sandgum/Triangulate-ES_01-Watch/CAD/Components (DON'T PRINT)/100mah battery (4).step

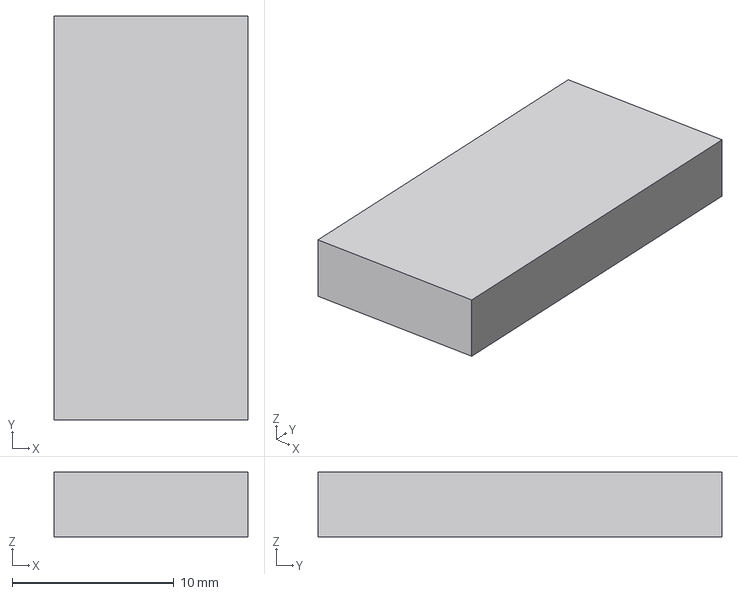
[picture p16: CAD file, 2026-01-16]
CAD/Components (DON'T PRINT)/100mah battery (4).step
12.0 x 25.0 x 4.00 mm
