sandgum/Triangulate-ES_01-Watch/CAD/Components (DON'T PRINT)/Button.step

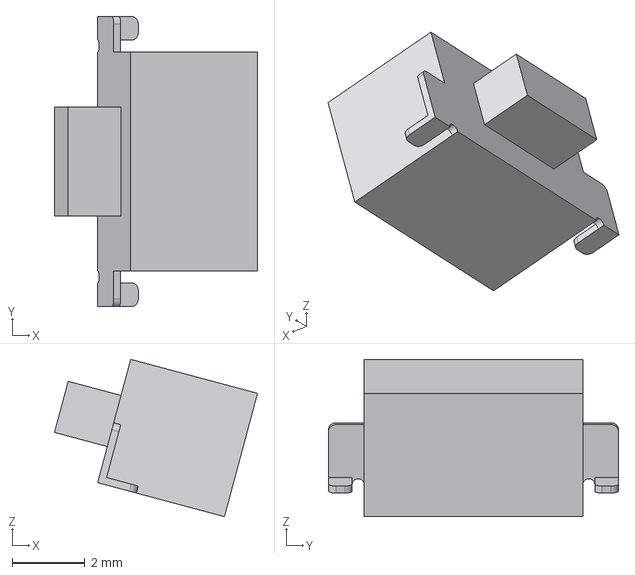
[picture p17: CAD file, 2026-01-16]
CAD/Components (DON'T PRINT)/Button.step
5.57 x 7.95 x 4.31 mm
