sandgum/Triangulate-ES_01-Watch/CAD/Components (DON'T PRINT)/oled display (1).step

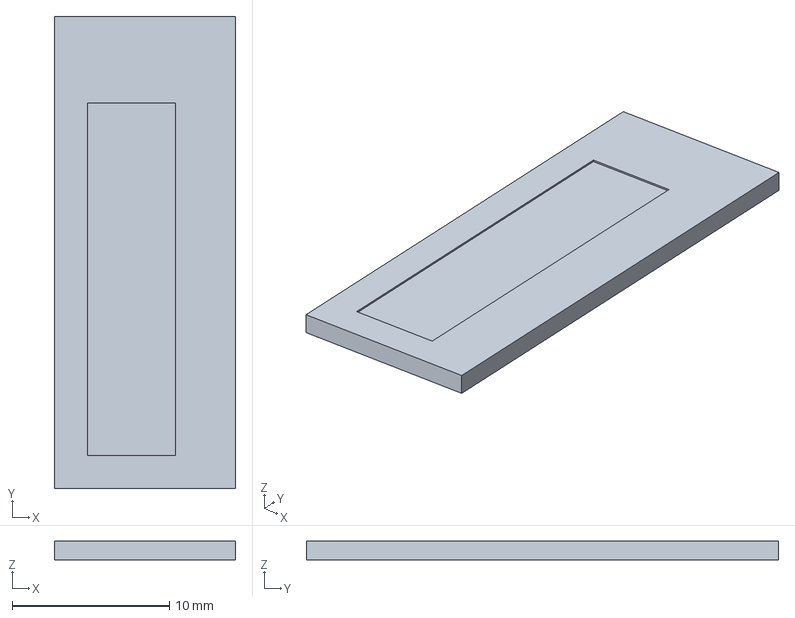
[picture p18: CAD file, 2026-01-16]
CAD/Components (DON'T PRINT)/oled display (1).step
11.5 x 30.0 x 1.20 mm
