sandgum/Triangulate-ES_01-Watch/CAD/Components (DON'T PRINT)/haptic motor.step

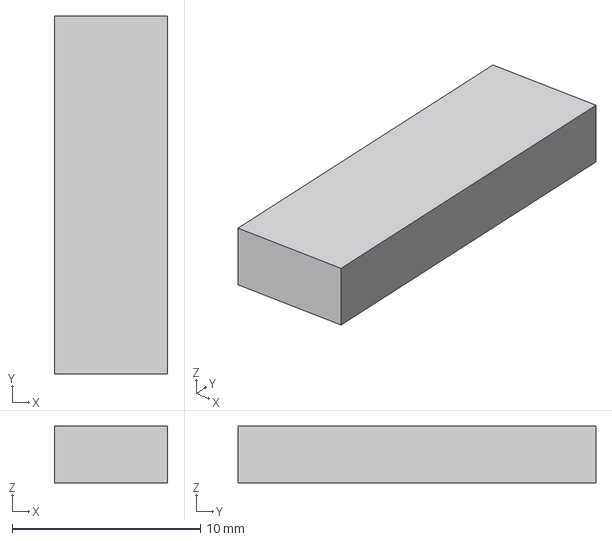
[picture p19: CAD file, 2026-01-16]
CAD/Components (DON'T PRINT)/haptic motor.step
6.00 x 19.0 x 3.00 mm
