sandgum/Triangulate-ES_01-Watch/CAD/Components (DON'T PRINT)/e ink display.step

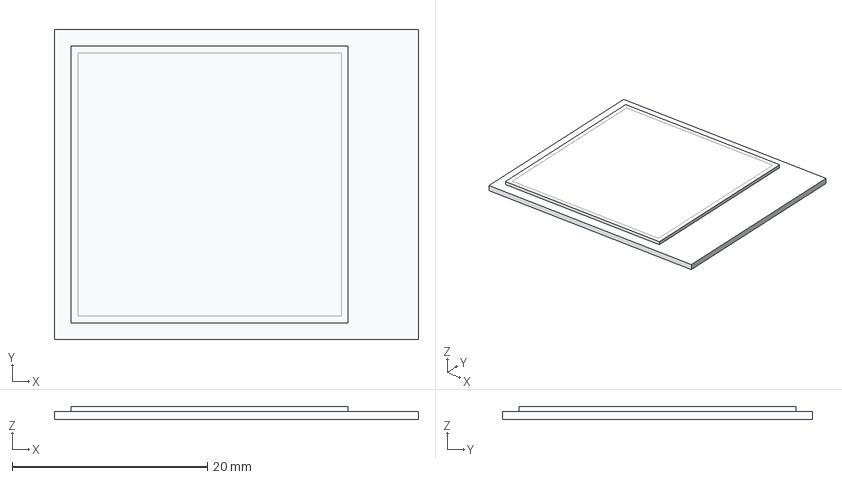
[picture p20: CAD file, 2026-01-16]
CAD/Components (DON'T PRINT)/e ink display.step
37.3 x 31.8 x 1.35 mm
