sandgum/Triangulate-ES_01-Watch/KiCad Files V1/E-ink watch.kicad_sch

## KiCad design KiCad Files V1/E-ink watch.kicad_sch (2025-12-14)

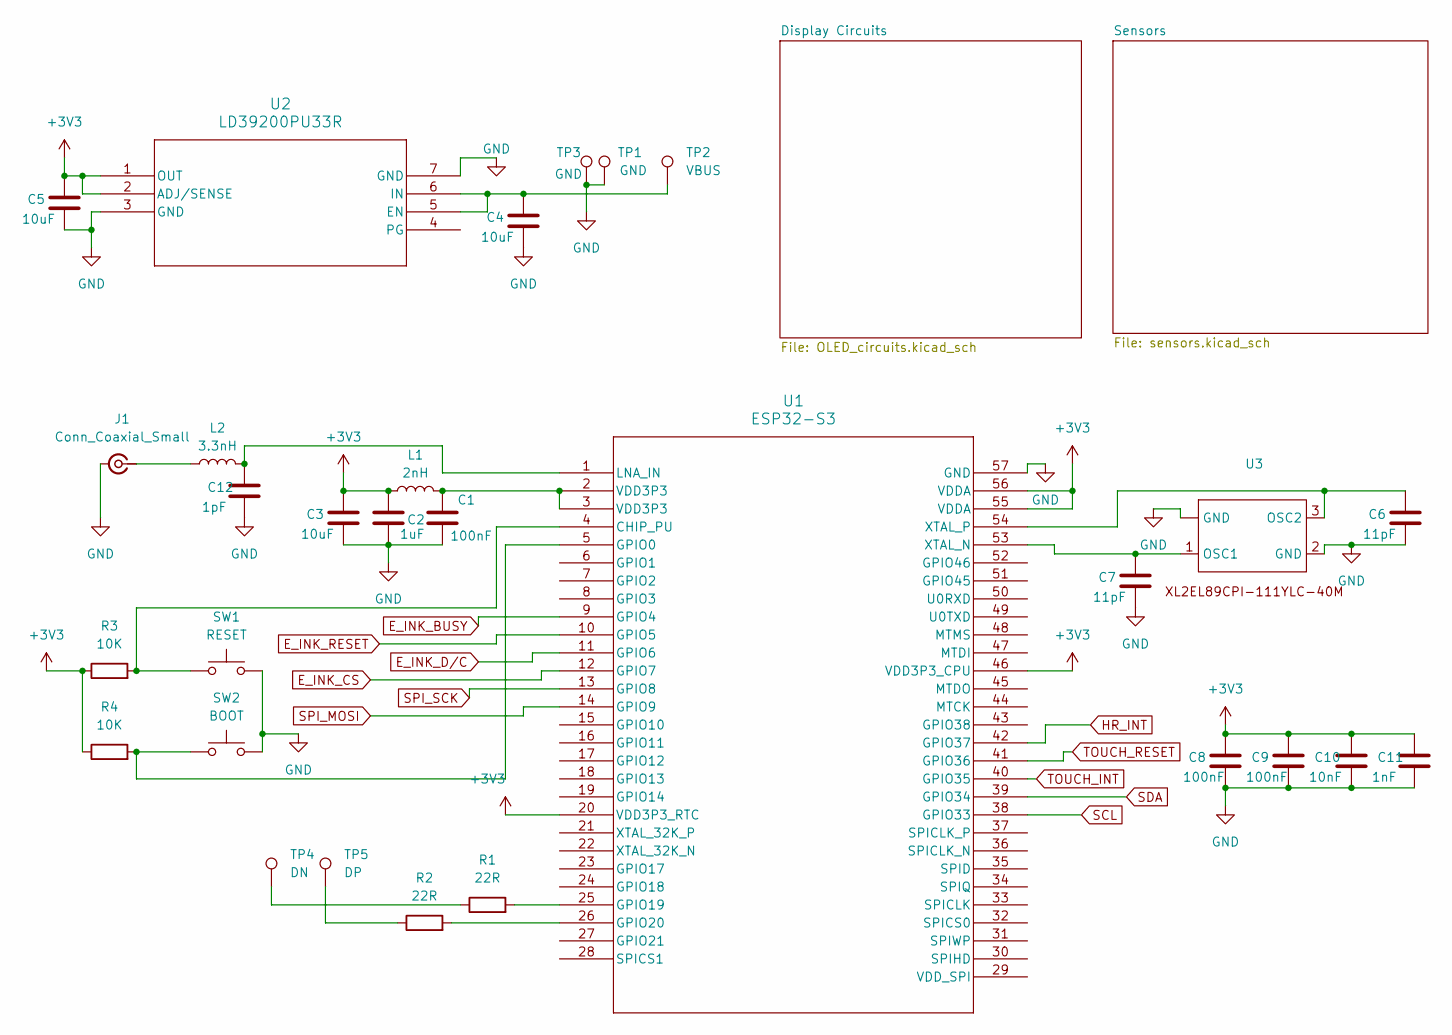
[picture p35: schematic E-ink watch.kicad_sch]

Parts:
C1, C8, C9: 100nF
C2: 1uF
C3, C4, C5: 10uF
C6, C7: 11pF
C10: 10nF
C11: 1nF
C12: 1pF
J1: Conn_Coaxial_Small
L1: 2nH
L2: 3.3nH
R1, R2: 22R
R3, R4: 10K
SW1: RESET
SW2: BOOT
TP1, TP3: GND
TP2: VBUS
TP4: DN
TP5: DP
U1: ESP32-S3; QFN56_7X7_EXP
U2: LD39200PU33R; SON_DFN6_3X3_STM
U3: (no value)

Connections:
+3V3: C2.1, C3.1, C5.1, C8.1, C9.1, C10.1, C11.1, L1.1, R3.1, R4.1, U1.20 (VDD3P3_RTC), U1.46 (VDD3P3_CPU), U1.55 (VDDA), U1.56 (VDDA), U2.1 (OUT), U2.2 (ADJ/SENSE)
E_INK_BUSY: U1.9 (GPIO4)
E_INK_CS: U1.12 (GPIO7)
E_INK_D/C: U1.11 (GPIO6)
E_INK_RESET: U1.10 (GPIO5)
GND: C1.2, C2.2, C3.2, C4.2, C5.2, C6.2, C7.2, C8.2, C9.2, C10.2, C11.2, C12.2, J1.2 (Ext), SW1.2, SW2.2, TP1.1, TP3.1, U1.57 (GND), U2.3 (GND), U2.7 (GND), U3. (GND), U3.2 (GND)
HR_INT: U1.42 (GPIO37)
unnamed: C1.1, L1.2, U1.2 (VDD3P3), U1.3 (VDD3P3)
unnamed: C4.1, TP2.1, U2.5 (EN), U2.6 (IN)
unnamed: C6.1, U1.54 (XTAL_P), U3.3 (OSC2)
unnamed: C7.1, U1.53 (XTAL_N), U3.1 (OSC1)
unnamed: C12.1, L2.2, U1.1 (LNA_IN)
unnamed: J1.1 (In), L2.1
unnamed: R1.1, TP4.1
unnamed: R1.2, U1.25 (GPIO19)
unnamed: R2.1, TP5.1
unnamed: R2.2, U1.26 (GPIO20)
unnamed: R3.2, SW1.1, U1.4 (CHIP_PU)
unnamed: R4.2, SW2.1, U1.5 (GPIO0)
SCL: U1.38 (GPIO33)
SDA: U1.39 (GPIO34)
SPI_MOSI: U1.14 (GPIO9)
SPI_SCK: U1.13 (GPIO8)
TOUCH_INT: U1.40 (GPIO35)
TOUCH_RESET: U1.41 (GPIO36)
