sandgum/Triangulate-ES_01-Watch/KiCad Files V1/OLED_circuits.kicad_sch

## KiCad design KiCad Files V1/OLED_circuits.kicad_sch (2025-12-14)

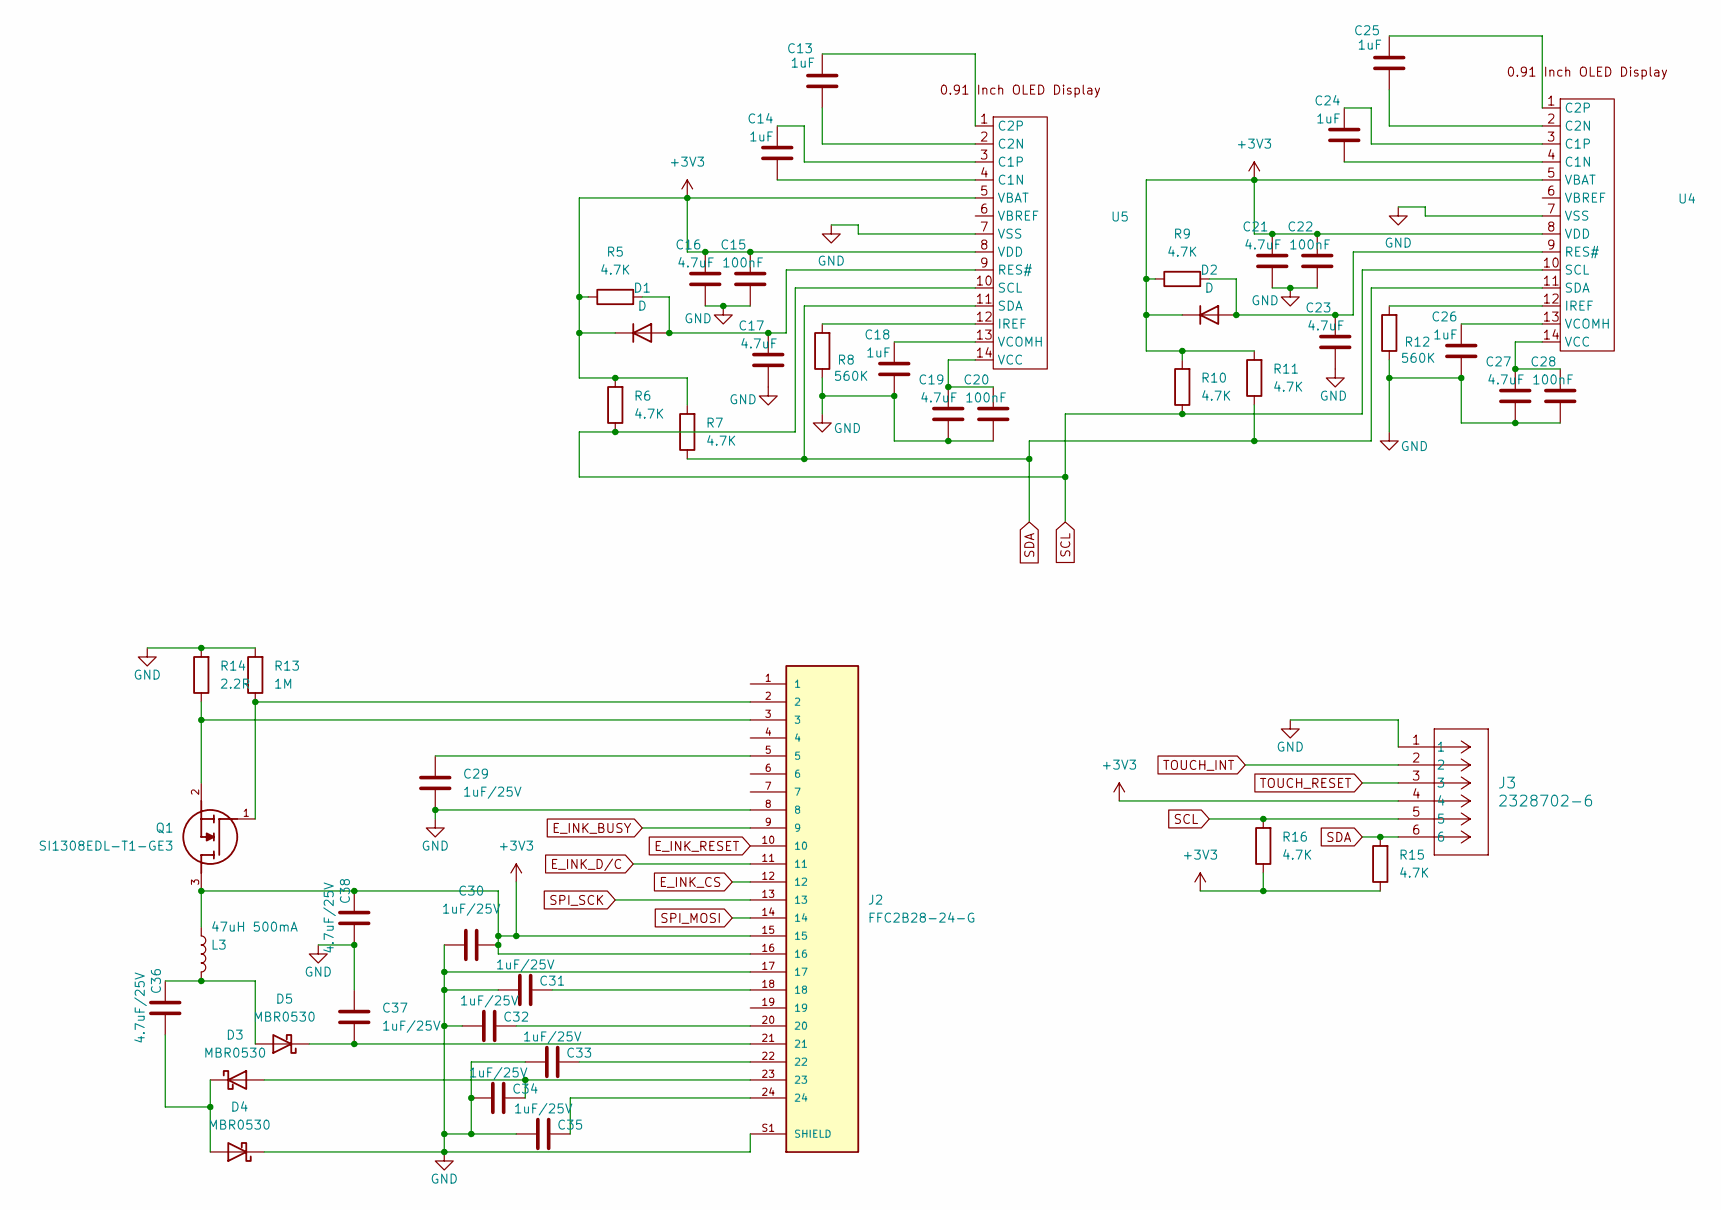
[picture p36: schematic OLED_circuits.kicad_sch]

Parts:
C13, C14, C18, C24, C25, C26: 1uF
C15, C20, C22, C28: 100nF
C16, C17, C19, C21, C23, C27: 4.7uF
C29, C30, C31, C32, C33, C34, C35, C37: 1uF/25V
C36, C38: 4.7uF/25V
D1, D2: D
D3, D4, D5: MBR0530
J2: FFC2B28-24-G; GCT_FFC2B28-24-G; PARTREV A
J3: 2328702-6; CONN6_2328702-6_TEC
L3: 47uH 500mA
Q1: SI1308EDL-T1-GE3; SOT65P210X110-3N; Mouser_Part_Number 78-SI1308EDL-T1-GE3
R5, R6, R7, R9, R10, R11, R15, R16: 4.7K
R8, R12: 560K
R13: 1M
R14: 2.2R
U4, U5: (no value)

Connections:
+3V3: C15.1, C16.1, C21.1, C22.1, C30.2, C38.2, D1.1 (K), D2.1 (K), J2.15, J2.16, J3.4, L3.1, Q1.3, R5.1, R6.2, R7.2, R9.1, R10.2, R11.2, R15.1, R16.1, U4.5 (VBAT), U4.8 (VDD), U5.5 (VBAT), U5.8 (VDD)
E_INK_BUSY: J2.9
E_INK_CS: J2.12
E_INK_D/C: J2.11
E_INK_RESET: J2.10
GND: C15.2, C16.2, C17.2, C18.2, C19.2, C20.2, C21.2, C22.2, C23.2, C26.2, C27.2, C28.2, C29.2, C30.1, C31.1, C32.1, C33.1, C34.1, C35.1, C37.1, C38.1, D4.1 (K), J2.8, J2.17, J2.S1 (SHIELD), J2.S2 (SHIELD), J3.1, R8.1, R12.1, R13.2, R14.2, U4.7 (VSS), U5.7 (VSS)
unnamed: C13.1, U5.1 (C2P)
unnamed: C13.2, U5.2 (C2N)
unnamed: C14.1, U5.3 (C1P)
unnamed: C14.2, U5.4 (C1N)
unnamed: C17.1, D1.2 (A), R5.2, U5.9 (RES#)
unnamed: C18.1, U5.13 (VCOMH)
unnamed: C19.1, C20.1, U5.14 (VCC)
unnamed: C23.1, D2.2 (A), R9.2, U4.9 (RES#)
unnamed: C24.1, U4.3 (C1P)
unnamed: C24.2, U4.4 (C1N)
unnamed: C25.1, U4.1 (C2P)
unnamed: C25.2, U4.2 (C2N)
unnamed: C26.1, U4.13 (VCOMH)
unnamed: C27.1, C28.1, U4.14 (VCC)
unnamed: C29.1, J2.5
unnamed: C31.2, J2.18
unnamed: C32.2, J2.20
unnamed: C33.2, J2.22
unnamed: C34.2, D3.2 (A), J2.23
unnamed: C35.2, J2.24
unnamed: C36.1, D3.1 (K), D4.2 (A)
unnamed: C36.2, D5.2 (A), L3.2
unnamed: C37.2, D5.1 (K), J2.21
unnamed: J2.2, Q1.1, R13.1
unnamed: J2.3, Q1.2, R14.1
unnamed: R8.2, U5.12 (IREF)
unnamed: R12.2, U4.12 (IREF)
SCL: J3.5, R6.1, R10.1, R16.2, U4.10 (SCL), U5.10 (SCL)
SDA: J3.6, R7.1, R11.1, R15.2, U4.11 (SDA), U5.11 (SDA)
SPI_MOSI: J2.14
SPI_SCK: J2.13
TOUCH_INT: J3.2
TOUCH_RESET: J3.3
