sandgum/Triangulate-ES_01-Watch/KiCad Files V1/sensors.kicad_sch

## KiCad design KiCad Files V1/sensors.kicad_sch (2025-12-14)

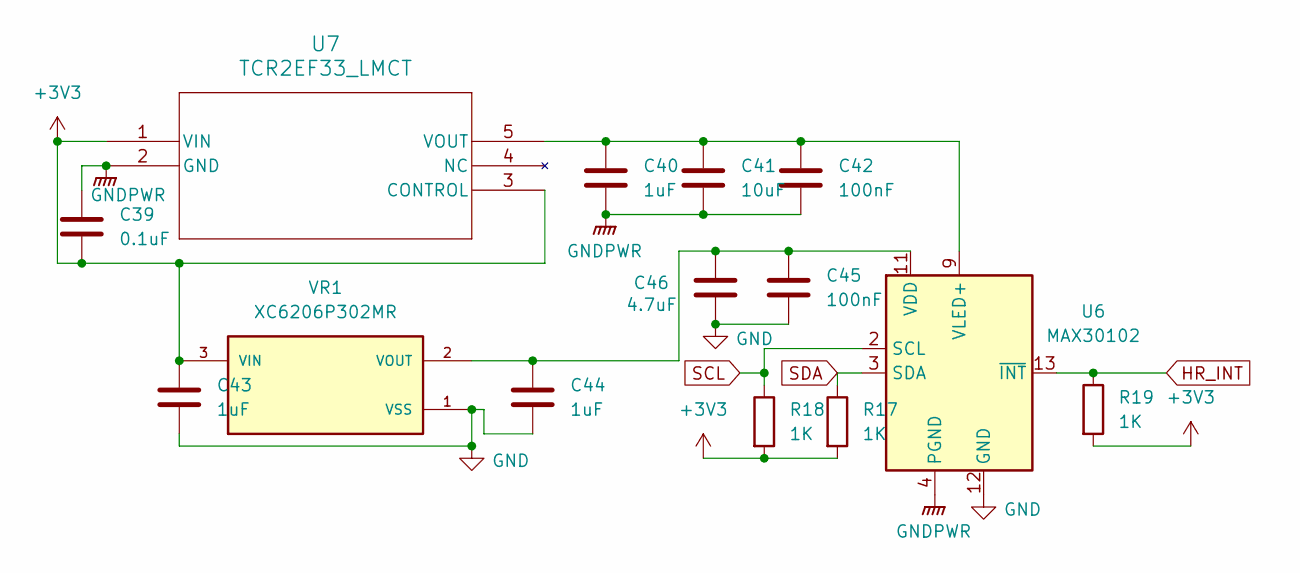
[picture p37: schematic sensors.kicad_sch]

Parts:
C39: 0.1uF
C40, C43, C44: 1uF
C41: 10uF
C42, C45: 100nF
C46: 4.7uF
R17, R18, R19: 1K
U6: MAX30102; Maxim_OLGA-14_3.3x5.6mm_P0.8mm
U7: TCR2EF33_LMCT; SOT-25 SMV_TOS
VR1: XC6206P302MR; SOT95P280X130-3N; PARTREV N/A

Connections:
+3V3: C39.2, C43.1, R17.2, R18.2, R19.2, U7.1 (VIN), U7.3 (CONTROL), VR1.3 (VIN)
GND: C43.2, C44.2, C45.2, C46.2, U6.12 (GND), VR1.1 (VSS)
GNDPWR: C39.1, C40.2, C41.2, C42.2, U6.4 (PGND), U7.2 (GND)
HR_INT: R19.1, U6.13 (~INT)
unnamed: C40.1, C41.1, C42.1, U6.9 (VLED+), U6.10 (VLED+), U7.5 (VOUT)
unnamed: C44.1, C45.1, C46.1, U6.11 (VDD), VR1.2 (VOUT)
SCL: R18.1, U6.2 (SCL)
SDA: R17.1, U6.3 (SDA)
